dcooperdalrymple/rpi-pico-drum/hardware/rpi-pico-drum.kicad_pcb

## KiCad design routed/keyboard-left.kicad_pcb

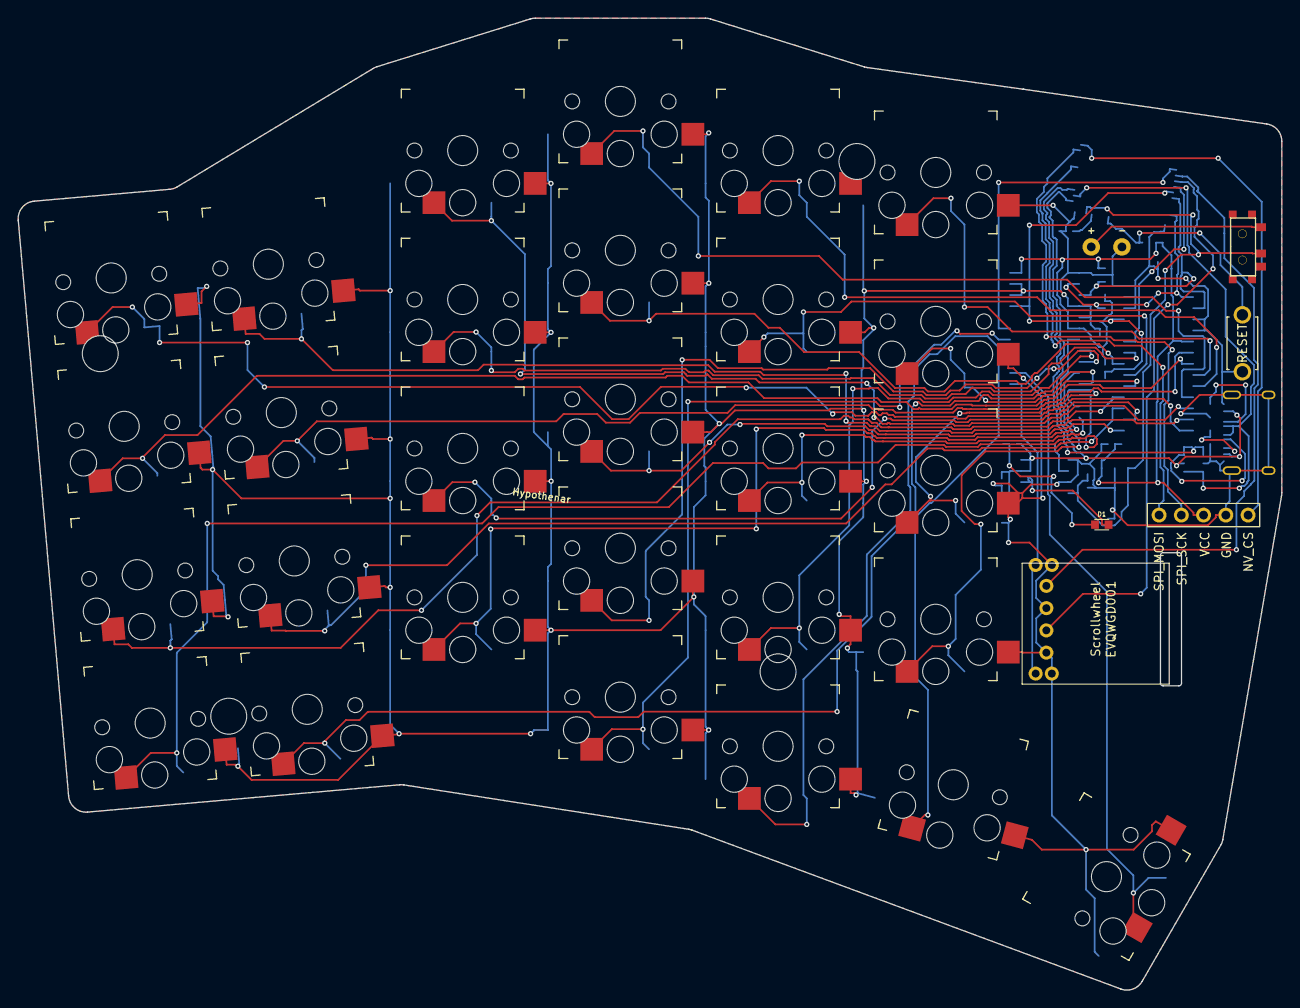
[picture p6: board keyboard-left.kicad_pcb from above]

Board: 2 copper layers, 144.2 x 110.9 mm, 60 parts (0 on the bottom side), 50 nets.

Parts:
19.051: ms88sf3
19.052, 19.053: MCP23017; MCP23017_SOIC-28W
19.054: USB_C_Receptacle_HRO_TYPE-C-31-M-12
19.055: USBLC6-2SC6; USBLC6-2SC6_SOT-23-6
19.056: TP4056; TP4056_SOP-8
19.057: XC6206P332MR; XC6206_SOT-89-3
BT1: BATTERY; battery_pads
DISP1: display_nice_view
P1: C1; passive_0603
P2: C2; passive_0603
P3: C3; passive_0603
P4: C4; passive_0603
P5: C5; passive_0603
P6: C6; passive_0603
P7: C7; passive_0603
P8: C8; passive_0603
P9: R1; passive_0603
P10: R2; passive_0603
P11: R3; passive_0603
P12: R4; passive_0603
P13: R5; passive_0603
P14: R6; passive_0603
P15: R7; passive_0603
P16: R8; passive_0603
P17: D1; passive_0603
S1, S2, S3, S4, S5, S6, S7, S8, S9, S10, S11, S12, S13, S14, S15, S16, S17, S18, S19, S20, S21, S22, S23, S24, S25, S26, S27, S28: PG1350
T1: SPDT_C128955
_1: ResetSW
_2, _3, _4, _5: Hole

Connections:
CHARGE_ACTIVE: 19.056.6, P17.2
CHG_LED: P16.2, P17.1
GND: 19.051.1, 19.051.18, 19.051.34, 19.052.10, 19.052.11, 19.052.14, 19.052.15, 19.052.16, 19.052.17, 19.053.10, 19.053.11, 19.053.14, 19.053.16, 19.053.17, 19.054.A1, 19.054.A12, 19.054.B1, 19.054.B12, 19.054.SH, 19.055.2, 19.056.1, 19.056.3, 19.057.2, BT1.2, DISP1.4, P1.2, P2.2, P3.2, P4.2, P5.2, P6.2, P7.2, P8.2, P11.2, P12.2, P13.2, S1.2, S2.2, S3.2, S4.2, S5.2, S6.2, S7.2, S8.2, S9.2, S10.2, S11.2, S12.2, S13.2, S14.2, S15.2, S16.2, S17.2, S18.2, S19.2, S20.2, S21.2, S22.2, S23.2, S24.2, S25.2, S26.2, S27.2, S28.2, _1.2
I2C_RESET: 19.051.13, 19.052.18, 19.053.18, P14.2
I2C_SCL: 19.051.14, 19.052.12, 19.053.12, P9.2
I2C_SDA: 19.051.17, 19.052.13, 19.053.13, P10.2
MCP_A_INT: 19.051.12, 19.052.20
MCP_B_INT: 19.051.9, 19.053.20
NV_CS: 19.051.45, DISP1.5
PROG: 19.056.2, P13.1
RESET: 19.051.28, P15.2, _1.1
SPI_MOSI: 19.051.41, DISP1.1
SPI_SCK: 19.051.44, DISP1.2
USB_CC1: 19.054.A5, P11.1
USB_CC2: 19.054.B5, P12.1
USB_DM: 19.051.36, 19.054.A7, 19.054.B7, 19.055.3, 19.055.4
USB_DP: 19.051.37, 19.054.A6, 19.054.B6, 19.055.1, 19.055.6
VBAT: 19.051.32, 19.056.4, 19.057.1, P3.1, P4.1, T1.2
VBAT_SW: BT1.1, T1.1
VBUS: 19.051.35, 19.054.A4, 19.054.A9, 19.054.B4, 19.054.B9, 19.055.5, 19.056.7, 19.056.8, P1.1, P2.1, P16.1
VCC: 19.052.9, 19.053.9, 19.053.15, 19.057.3, DISP1.3, P5.1, P7.1, P8.1, P9.1, P10.1, P14.1, P15.1
VDD_MCU: 19.051.31, P6.1
sw_matrix_index_bottom: 19.053.7, S19.1
sw_matrix_index_home: 19.053.1, S20.1
sw_matrix_index_mod: 19.053.22, S18.1
sw_matrix_index_num: 19.052.5, S22.1
sw_matrix_index_top: 19.052.23, S21.1
sw_matrix_inner_bottom: 19.053.8, S23.1
sw_matrix_inner_home: 19.053.2, S24.1
sw_matrix_inner_num: 19.052.6, S26.1
sw_matrix_inner_top: 19.052.24, S25.1
sw_matrix_middle_bottom: 19.053.6, S14.1
sw_matrix_middle_home: 19.052.28, S15.1
sw_matrix_middle_mod: 19.053.21, S13.1
sw_matrix_middle_num: 19.052.4, S17.1
sw_matrix_middle_top: 19.052.22, S16.1
sw_matrix_outer_bottom: 19.053.3, S1.1
sw_matrix_outer_home: 19.052.25, S2.1
sw_matrix_outer_num: 19.052.1, S4.1
sw_matrix_outer_top: 19.052.7, S3.1
sw_matrix_pinky_bottom: 19.053.4, S5.1
sw_matrix_pinky_home: 19.052.26, S6.1
sw_matrix_pinky_num: 19.052.2, S8.1
sw_matrix_pinky_top: 19.052.8, S7.1
sw_matrix_ring_bottom: 19.053.5, S9.1
sw_matrix_ring_home: 19.052.27, S10.1
sw_matrix_ring_num: 19.052.3, S12.1
sw_matrix_ring_top: 19.052.21, S11.1
sw_thumbs_layer_cluster: 19.053.23, S27.1
sw_thumbs_space_cluster: 19.053.24, S28.1
